coseyfannitutti/discipline/acrylic-case/discipline-foot-3.dxf

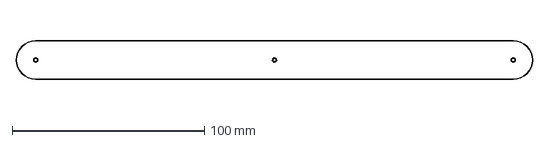
[picture p24: CAD file, 2020-04-20]
acrylic-case/discipline-foot-3.dxf
268.5 x 20.0 mm
