coseyfannitutti/discipline/acrylic-case/discipline-bottom.dxf

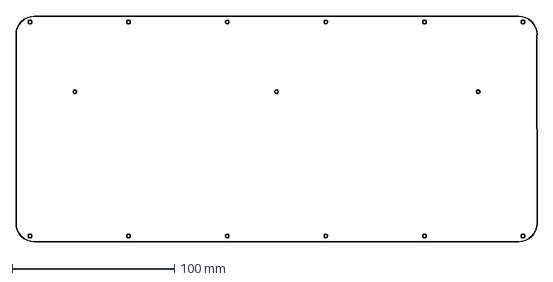
[picture p25: CAD file, 2020-04-20]
acrylic-case/discipline-bottom.dxf
320.9 x 138.8 mm
