coseyfannitutti/discipline/acrylic-case/discipline-open-layer.dxf

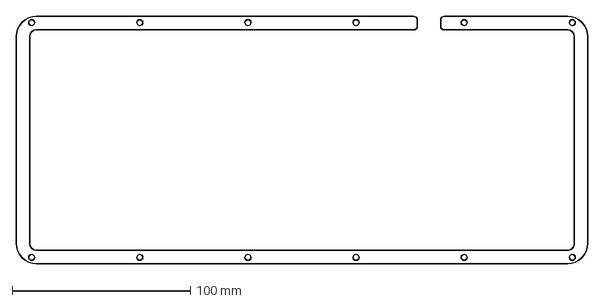
[picture p26: CAD file, 2020-04-20]
acrylic-case/discipline-open-layer.dxf
320.9 x 138.8 mm
