coseyfannitutti/discipline/acrylic-case/discipline-closed-layer.dxf

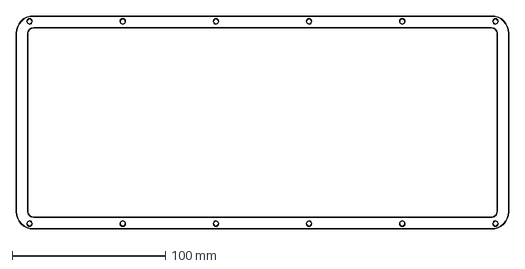
[picture p27: CAD file, 2020-04-20]
acrylic-case/discipline-closed-layer.dxf
320.9 x 138.8 mm
