coseyfannitutti/discipline/acrylic-case/discipline-foot-2.dxf

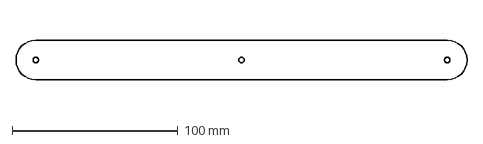
[picture p28: CAD file, 2020-04-20]
acrylic-case/discipline-foot-2.dxf
272.5 x 24.0 mm
